GeoffreyKassis/led_grow_light/docs/review/final-m-schematic.png

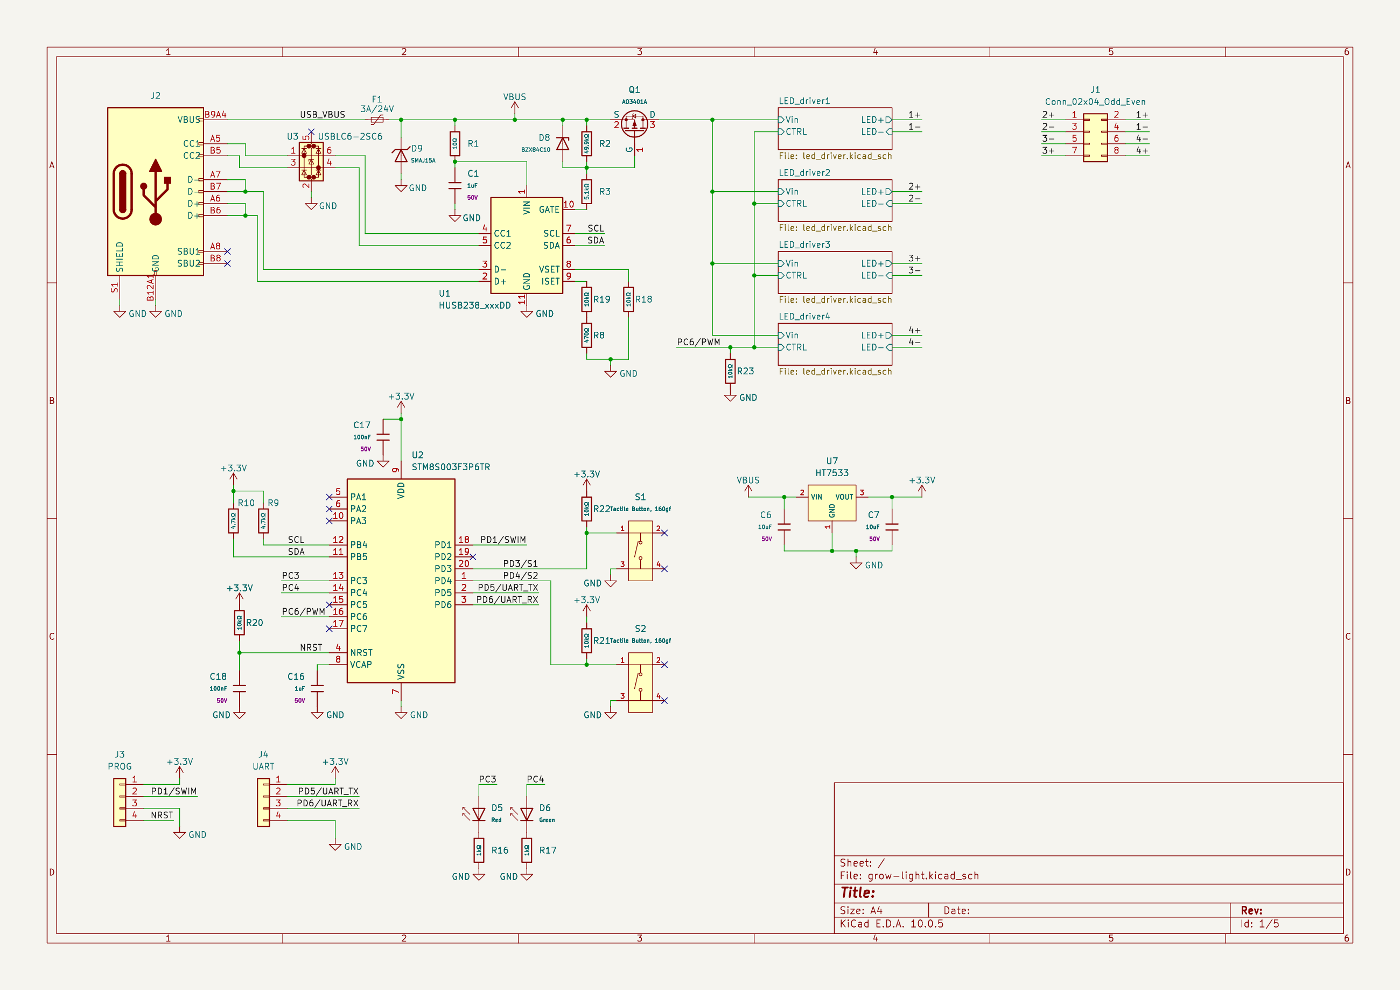
docs/review/final-m-schematic.png
